mslinklater/LINK_01/images/20210213_121410.jpg

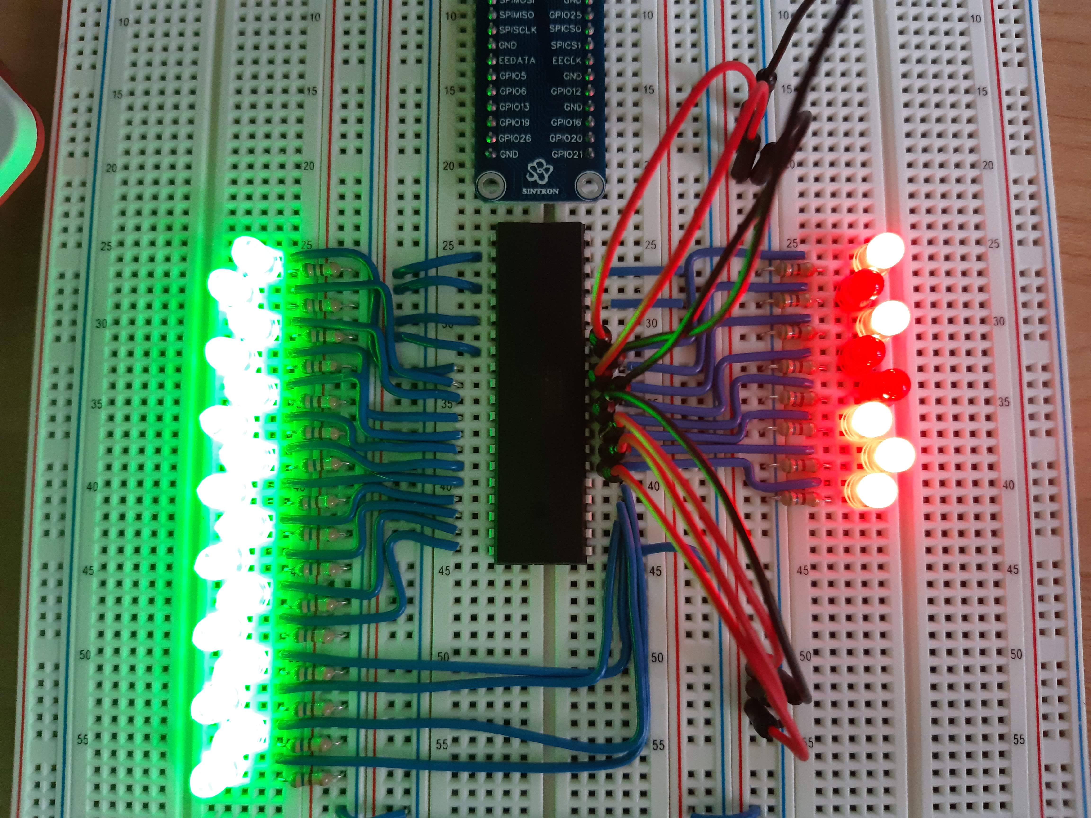
images/20210213_121410.jpg
