mslinklater/LINK_01/code/pico/system.c

#include "system.h"
#include "ic6502.h"
#include "uart.h"
#include "shifter.h"

static uint64_t tickDelayMicroSeconds;
static bool fQuit = false;

static uint64_t tickDelay = 500000;
static uint64_t oldTickDelay = 0;

void system_main()
{
	uart_ready();
	while(!fQuit)
	{
		if(tickDelay > 0)
		{
			ic6502_tick(tickDelay);
		}
		uart_update();

	}
}

void system_halt()
{
	if(tickDelay > 0)
	{
		oldTickDelay = tickDelay;
		tickDelay = 0;
	}
}

void system_continue()
{
	tickDelay = oldTickDelay;
}

void system_clock_tick()
{

}

void system_set_tick_rate(int rate)
{
	tickDelay = 1000000 / rate;

	int bp=0;
	bp++;
}

uint8_t system_read_memory(uint16_t address)
{
	return 0;
}

void system_write_memory(uint16_t address, uint8_t data)
{

}
