mslinklater/LINK_01/code/pico/ic6502.h

#include "pico/stdlib.h"

extern void ic6502_init();
extern void ic6502_reset();

extern void ic6502_enable_bus(bool enable);

// Ideally only call this from system.c
extern void ic6502_tick(uint64_t microSeconds);
