mslinklater/LINK_01/code/pico/test.c

#include "pico/stdlib.h"
#include "test.h"
#include "configuration.h"
#include "ic6502.h"
#include "shifter.h"
#include "busmaster.h"

void do6502Test(int iter)
{
    while (iter-- > 0) 
	{
		ic6502_tick(10000);
	}
}

void doShifterTest(int iter)
{
	shifter_init();

	while(true)
	{
		gpio_put(SHIFTER_IN_PIN, 1);
		for(int i=0 ; i<8 ; i++)
		{
			ic6502_tick(10000);
			ic6502_tick(10000);
		}
		gpio_put(SHIFTER_IN_PIN, 0);
		for(int i=0 ; i<8 ; i++)
		{
			ic6502_tick(10000);
			ic6502_tick(10000);
		}
	}
}

void runTest()
{
//	busmaster_set_control(BUSMASTER_CONTROL_OFF);
//	sleep_ms(1000);
//	busmaster_set_control(BUSMASTER_CONTROL_SHIFTER);
//	sleep_ms(1000);
//	busmaster_set_control(BUSMASTER_CONTROL_6502);
//	sleep_ms(1000);

	busmaster_set_control(BUSMASTER_CONTROL_6502);
	do6502Test(99999999);

	busmaster_set_control(BUSMASTER_CONTROL_SHIFTER);
	doShifterTest(1000000);
}
